nickbild/vectron_ai/media/down_large.bmp

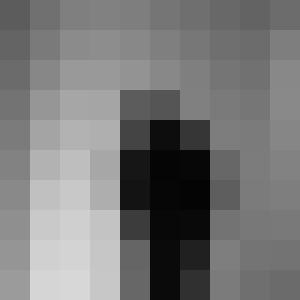
media/down_large.bmp
