nickbild/vectron_ai/media/right_large.bmp

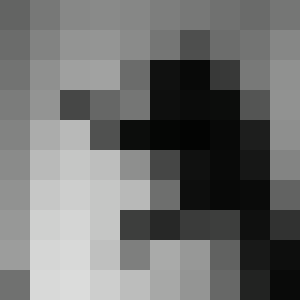
media/right_large.bmp
